DavidM42/channel4/user/video_broadcast.c

/******************************************************************************
 * Copyright 2013-2015 Espressif Systems
 *           2015 <>< Charles Lohr
 * 			 2022 Paul Schlarmann
 *
 * FileName: i2s_freertos.c
 *
 * Description: I2S output routines for a FreeRTOS system. Uses DMA and a queue
 * to abstract away the nitty-gritty details.
 *
 * Modification history:
 *     2015/06/01, v1.0 File created.
 *     2015/07/23, Switch to making it a WS2812 output device.
 *     2016/01/28, Modified to re-include TX_ stuff.
 *     2022/09/26, Modified CNLohrs code to also allow PAL broadcast
*******************************************************************************

Notes:

 This is pretty badly hacked together from the MP3 example.
 I spent some time trying to strip it down to avoid a lot of the TX_ stuff. 
 That seems to work.

 Major suggestions that I couldn't figure out:
	* Use interrupts to disable DMA, so it isn't running nonstop.
    * Use interrupts to flag when new data can be sent.

 When I try using interrupts, it seems to work for a bit but things fall apart
 rather quickly and the engine just refuses to send anymore until reboot.

 The way it works right now is to keep the DMA running forever and just update
 the data in the buffer so it continues sending the frame.

Extra copyright info:
  Actually not much of this file is Copyright Espressif, comparativly little
  mostly just the stuff to make the I2S bus go.

*******************************************************************************/


#include "slc_register.h"
#include "esp82xxutil.h"
#include <c_types.h>
#include "video_broadcast.h"
#include "user_interface.h"
#include "../tablemaker/broadcast_tables.h"
#include <dmastuff.h>

#define FUNC_I2SO_DATA                      1
#define FUNC_U0RXD                          0  //What the pin is after reset: the UART's receive line.

#define WS_I2S_BCK 1  //Can't be less than 1.
#define WS_I2S_DIV 2

#ifdef PAL
  #define LINE_BUFFER_LENGTH 160

  /* PAL signals */
  #define SHORT_SYNC_INTERVAL    5
  #define LONG_SYNC_INTERVAL    75
  #define NORMAL_SYNC_INTERVAL  10
  #define LINE_SIGNAL_INTERVAL 150

  #define COLORBURST_INTERVAL 10
#else
  #define LINE_BUFFER_LENGTH 159

  /* NTSC signals */
  #define SHORT_SYNC_INTERVAL    6
  #define LONG_SYNC_INTERVAL    73
  #define SERRATION_PULSE_INT   67
  #define NORMAL_SYNC_INTERVAL  12
  #define LINE_SIGNAL_INTERVAL 147

  #define COLORBURST_INTERVAL 4
#endif

//Sync, colorburst and black before the framebuffer starts on a line.
#define HDR_SPD (NORMAL_SYNC_INTERVAL+1+COLORBURST_INTERVAL+11)

//How many picture lines (FT_LIN) the line table in CbTable hands out per field, at least.
#ifdef PAL
  #define PICTURE_LINES 265
#else
  #define PICTURE_LINES 210
#endif

//A framebuffer with fewer lines than that sits in the middle, with black lines above and below it.
#if FBH < PICTURE_LINES
  #define FB_TOP ((PICTURE_LINES-FBH)/2)
#else
  #define FB_TOP 0
#endif

#ifdef WHITE_BORDER
  //Fills the visible area left, right and above the framebuffer with something bright instead of black.  TVs that don't
  //hold their black level (most small black and white ones) show a mostly dark picture as gray, this gives them something
  //bright to go by.  Left/right are in 32-bit words and stay clear of the porches, the top lines skipped are the ones in
  //vertical blanking.  The lines below the picture stay black: bright lines running right up to vertical sync made the
  //whole picture bounce on the TV this was tried on.
  //BORDER_LEVEL is the color to use.  White is the brightest, but it glows.
  #ifndef BORDER_LEVEL
    #define BORDER_LEVEL WHITE_LEVEL
  #endif
  #ifdef PAL
    #define BORDER_LEFT      5
    #define BORDER_RIGHT     7
    #define BORDER_SKIP_TOP 18
  #else
    #define BORDER_LEFT      4
    #define BORDER_RIGHT    10
    #define BORDER_SKIP_TOP 13
  #endif
#endif

#define I2SDMABUFLEN (LINE_BUFFER_LENGTH)		//Length of one buffer, in 32-bit words.
//#define LINE16LEN (I2SDMABUFLEN*2)
#define LINE32LEN I2SDMABUFLEN

//Bit clock @ 80MHz = 12.5ns
//Word clock = 400ns
//Each NTSC line = 15,734.264 Hz.  63556 ns
//Each group of 4 bytes = 

#define LINETYPES 6

int8_t jam_color = -1; 
uint8_t video_transmitting; //Is the TV signal on the RX pin right now?  Set with VideoTransmit().

//WS_I2S_DIV - if 1 will actually be 2.  Can't be less than 2.

//		CLK_I2S = 160MHz / I2S_CLKM_DIV_NUM
//		BCLK = CLK_I2S / I2S_BCK_DIV_NUM
//		WS = BCLK/ 2 / (16 + I2S_BITS_MOD)
//		Note that I2S_CLKM_DIV_NUM must be >5 for I2S data
//		I2S_CLKM_DIV_NUM - 5-127
//		I2S_BCK_DIV_NUM - 2-127



//I2S DMA buffer descriptors
static struct sdio_queue i2sBufDesc[DMABUFFERDEPTH];
uint32_t i2sBD[I2SDMABUFLEN*DMABUFFERDEPTH];

//Queue which contains empty DMA buffers

//This routine is called as soon as the DMA routine has something to tell us. All we
//handle here is the RX_EOF_INT status, which indicate the DMA has sent a buffer whose
//descriptor has the 'EOF' field set to 1.
int gline = 0;
int gframe = 0;
static int linescratch;
uint16_t framebuffer[((FBW2/4)*(FBH))*2];

const uint32_t * tablestart = &premodulated_table[0];
const uint32_t * tablept = &premodulated_table[0];
const uint32_t * tableend = &premodulated_table[PREMOD_ENTRIES*PREMOD_SIZE];
uint32_t * curdma;

uint16_t pixline; //line number currently being written out.  PAL has more than 255 of them.
#ifdef WHITE_BORDER
uint8_t marginline; //how many of the margin lines above the picture are out already.
#endif

//Each "qty" is 32 bits, or .4us
LOCAL void fillwith( uint16_t qty, uint8_t color )
{
//	return;
	//We're using this one.
	if( qty & 1 )
	{
		*(curdma++) = tablept[color]; tablept += PREMOD_SIZE;
	}
	qty>>=1;
	for( linescratch = 0; linescratch < qty; linescratch++ )
	{
		*(curdma++) = tablept[color]; tablept += PREMOD_SIZE;
		*(curdma++) = tablept[color]; tablept += PREMOD_SIZE;
		if( tablept >= tableend ) tablept = tablept - tableend + tablestart;
	}
}


//XXX TODO: Revisit the length of time the system is at SYNC, BLACK, etc.

LOCAL void FT_STA() // Short Sync
{
	pixline = 0; //Reset the framebuffer out line count (can be done multiple times)
#ifdef WHITE_BORDER
	marginline = 0;
#endif

	fillwith( SHORT_SYNC_INTERVAL, SYNC_LEVEL );
	fillwith( LONG_SYNC_INTERVAL, BLACK_LEVEL );
	fillwith( SHORT_SYNC_INTERVAL, SYNC_LEVEL );
	fillwith( LINE32LEN - (SHORT_SYNC_INTERVAL+LONG_SYNC_INTERVAL+SHORT_SYNC_INTERVAL), BLACK_LEVEL );
}


LOCAL void FT_STB() // Long Sync
{
	#ifdef PAL
		#define FT_STB_BLACK_INTERVAL SHORT_SYNC_INTERVAL
	#else
		#define FT_STB_BLACK_INTERVAL NORMAL_SYNC_INTERVAL
	#endif
	fillwith( LONG_SYNC_INTERVAL, SYNC_LEVEL );
	fillwith( FT_STB_BLACK_INTERVAL, BLACK_LEVEL );
	fillwith( LONG_SYNC_INTERVAL, SYNC_LEVEL );
	fillwith( LINE32LEN - (LONG_SYNC_INTERVAL+FT_STB_BLACK_INTERVAL+LONG_SYNC_INTERVAL), BLACK_LEVEL );
}

//Margin at top and bottom of screen (Mostly invisible)
//Closed Captioning would go somewhere in here, I guess?
LOCAL void FT_B() // Black
{
	fillwith( NORMAL_SYNC_INTERVAL, SYNC_LEVEL );
	fillwith( 2, BLACK_LEVEL );
	fillwith( COLORBURST_INTERVAL, COLORBURST_LEVEL );
#ifdef WHITE_BORDER
	//Above the picture and past vertical blanking.
	if( !pixline && marginline++ >= BORDER_SKIP_TOP )
	{
		fillwith( 10 - BORDER_LEFT, BLACK_LEVEL );
		fillwith( BORDER_LEFT + FBW2 + BORDER_RIGHT, BORDER_LEVEL );
		fillwith( LINE32LEN - (HDR_SPD+FBW2+BORDER_RIGHT), BLACK_LEVEL );
		return;
	}
#endif
	fillwith( LINE32LEN-NORMAL_SYNC_INTERVAL-2-COLORBURST_INTERVAL, (pixline<1)?GRAY_LEVEL:BLACK_LEVEL);
	//Gray seems to help sync if at top.  TODO: Investigate if white works even better!
}

LOCAL void FT_SRA() // Short to long
{
	fillwith( SHORT_SYNC_INTERVAL, SYNC_LEVEL );
	fillwith( LONG_SYNC_INTERVAL, BLACK_LEVEL );
	#ifdef PAL
	fillwith( LONG_SYNC_INTERVAL, SYNC_LEVEL );
	fillwith( LINE32LEN - (SHORT_SYNC_INTERVAL+LONG_SYNC_INTERVAL+LONG_SYNC_INTERVAL), BLACK_LEVEL );
	#else
	fillwith( SERRATION_PULSE_INT, SYNC_LEVEL );
	fillwith( LINE32LEN - (SHORT_SYNC_INTERVAL+LONG_SYNC_INTERVAL+SERRATION_PULSE_INT), BLACK_LEVEL );
	#endif
}

LOCAL void FT_SRB() // Long to short
{
	#ifdef PAL
	fillwith( LONG_SYNC_INTERVAL, SYNC_LEVEL );
	fillwith( SHORT_SYNC_INTERVAL, BLACK_LEVEL );
	fillwith( SHORT_SYNC_INTERVAL, SYNC_LEVEL );
	fillwith( LINE32LEN - (LONG_SYNC_INTERVAL+SHORT_SYNC_INTERVAL+SHORT_SYNC_INTERVAL), BLACK_LEVEL );
	#else
	fillwith( SERRATION_PULSE_INT, SYNC_LEVEL );
	fillwith( NORMAL_SYNC_INTERVAL, BLACK_LEVEL );
	fillwith( SHORT_SYNC_INTERVAL, SYNC_LEVEL );
	fillwith( LINE32LEN - (SERRATION_PULSE_INT+NORMAL_SYNC_INTERVAL+SHORT_SYNC_INTERVAL), BLACK_LEVEL );
	#endif
}

LOCAL void FT_LIN() // Line Signal
{
	//TODO: Make this do something useful.
	fillwith( NORMAL_SYNC_INTERVAL, SYNC_LEVEL );
	fillwith( 1, BLACK_LEVEL );
	fillwith( COLORBURST_INTERVAL, COLORBURST_LEVEL );

#if FBH < PICTURE_LINES
	//Lines the framebuffer does not reach, above and below it.
	if( (uint16_t)( pixline - FB_TOP ) >= FBH )
	{
#ifdef WHITE_BORDER
		if( pixline < FB_TOP )
		{
			fillwith( 11 - BORDER_LEFT, BLACK_LEVEL );
			fillwith( BORDER_LEFT + FBW2 + BORDER_RIGHT, BORDER_LEVEL );
			fillwith( LINE32LEN - (HDR_SPD+FBW2+BORDER_RIGHT), BLACK_LEVEL );
		}
		else
#endif
		{
			fillwith( LINE32LEN - (HDR_SPD-11), BLACK_LEVEL );
		}
		pixline++;
		return;
	}
#endif

#ifdef WHITE_BORDER
	fillwith( 11 - BORDER_LEFT, BLACK_LEVEL );
	fillwith( BORDER_LEFT, BORDER_LEVEL );
#else
	fillwith( 11, BLACK_LEVEL );
#endif

	int fframe = gframe & 1;
//#define FILLTEST
#ifdef FILLTEST

	fillwith( FBW/32, BLACK_LEVEL );
	fillwith( FBW/32, 1 );
	fillwith( FBW/32, 2 );
	fillwith( FBW/32, 3 );
	fillwith( FBW/32, 4 );
	fillwith( FBW/32, 5 );
	fillwith( FBW/32, 6 );
	fillwith( FBW/32, 0 );
	fillwith( FBW/32, 0 );
	fillwith( FBW/32, 0 );
	fillwith( FBW/32, 0 );
	fillwith( FBW/32, 0 );
	fillwith( FBW/8, BLACK_LEVEL );
	fillwith( LINE32LEN - (HDR_SPD+FBW/2), BLACK_LEVEL );

#else
	uint16_t * fbs = (uint16_t*)(&framebuffer[ ( ((pixline-FB_TOP) * (FBW2/2)) + ( ((FBW2/2)*(FBH))*(fframe)) ) / 2 ]);

	for( linescratch = 0; linescratch < FBW2/4; linescratch++ )
	{
		uint16_t fbb;
		fbb = fbs[linescratch];
		*(curdma++) = tablept[(fbb>>0)&15];		tablept += PREMOD_SIZE;
		*(curdma++) = tablept[(fbb>>4)&15];		tablept += PREMOD_SIZE;
		*(curdma++) = tablept[(fbb>>8)&15];		tablept += PREMOD_SIZE;
		*(curdma++) = tablept[(fbb>>12)&15];	tablept += PREMOD_SIZE;
		if( tablept >= tableend ) tablept = tablept - tableend + tablestart;
	}

#ifdef WHITE_BORDER
	fillwith( BORDER_RIGHT, BORDER_LEVEL );
	fillwith( LINE32LEN - (HDR_SPD+FBW2+BORDER_RIGHT), BLACK_LEVEL );
#else
	fillwith( LINE32LEN - (HDR_SPD+FBW2), BLACK_LEVEL); //WHITE_LEVEL );
#endif
#endif

	pixline++;
}

static uint32_t systimex = 0;
static uint32_t systimein = 0;
uint32_t last_internal_frametime;
LOCAL void FT_CLOSE_M() // End Frame
{
	#ifdef PAL
	fillwith( SHORT_SYNC_INTERVAL, SYNC_LEVEL );
	fillwith( LONG_SYNC_INTERVAL, BLACK_LEVEL );
	fillwith( SHORT_SYNC_INTERVAL, SYNC_LEVEL );
	fillwith( LINE32LEN - (SHORT_SYNC_INTERVAL+LONG_SYNC_INTERVAL+SHORT_SYNC_INTERVAL), BLACK_LEVEL );
	#else
	fillwith( NORMAL_SYNC_INTERVAL, SYNC_LEVEL );
	fillwith( 2, BLACK_LEVEL );
	fillwith( 4, COLORBURST_LEVEL );
	fillwith( LINE32LEN-NORMAL_SYNC_INTERVAL-6, WHITE_LEVEL );
	#endif
	gline = -1;
	gframe++;

	last_internal_frametime = systimex;
	systimex = 0;
	systimein = system_get_time();
}

#include "../tablemaker/CbTable.h" 

void (*CbTable[FT_MAX_d])() = { FT_STA, FT_STB, FT_B, FT_SRA, FT_SRB, FT_LIN, FT_CLOSE_M };

void slc_isr(void * v) {
	//portBASE_TYPE HPTaskAwoken=0;
	struct sdio_queue *finishedDesc;
	uint32 slc_intr_status;
	int x;

	slc_intr_status = READ_PERI_REG(SLC_INT_STATUS);
	//clear all intr flags
	WRITE_PERI_REG(SLC_INT_CLR, 0xffffffff);//slc_intr_status);
	if ( (slc_intr_status & SLC_RX_EOF_INT_ST))
	{
		//The DMA subsystem is done with this block: Push it on the queue so it can be re-used.
		finishedDesc=(struct sdio_queue*)READ_PERI_REG(SLC_RX_EOF_DES_ADDR);
		curdma = (uint32_t*)finishedDesc->buf_ptr;

		//Allow signal jamming, useful for testing output.
		if( jam_color < 0 )
		{
			//*startdma = premodulated_table[0];
			int lk = 0;
			if( gline & 1 )
				lk = (CbLookup[gline>>1]>>4)&0x0f;
			else
				lk = CbLookup[gline>>1]&0x0f;
	
			systimein = system_get_time();
			CbTable[lk]();
			systimex += system_get_time() - systimein;
			gline++;
		}
		else
		{
			fillwith( LINE32LEN, jam_color );
		}
	}
}

//Switches the TV signal on the RX pin on or off.
//The line generator keeps running either way, so the signal is there at once when it is switched on.  Off means the
//pin goes back to being the UART's receive line, so it carries no signal: the TV gets nothing, and the board's own
//WiFi is not disturbed by it.  While it is off, no screens get drawn either (see procTask in user_main.c).
void ICACHE_FLASH_ATTR VideoTransmit( int on )
{
	video_transmitting = on ? 1 : 0;

	if( on )
	{
		PIN_FUNC_SELECT(PERIPHS_IO_MUX_U0RXD_U, FUNC_I2SO_DATA);
	}
	else
	{
		PIN_FUNC_SELECT(PERIPHS_IO_MUX_U0RXD_U, FUNC_U0RXD);
	}
}

#ifdef RELAY_GPIO
#if RELAY_GPIO < 0 || RELAY_GPIO > 15 || RELAY_GPIO == 1 || RELAY_GPIO == 3 || ( RELAY_GPIO >= 6 && RELAY_GPIO <= 11 )
#error RELAY_GPIO has to be one of 0, 2, 4, 5, 12, 13, 14, 15.  1 and 3 are the serial lines (3 carries the TV signal), 6 to 11 belong to the flash chip.
#endif

//Switches the relay.  It is not tied to the TV signal: the signal goes off and on while a screen is filled
//(CH and CG), and the relay has to stay on through that.
void ICACHE_FLASH_ATTR RelaySet( int on )
{
	MakePinGPIO( RELAY_GPIO );
	GPIO_OUTPUT_SET( GPIO_ID_PIN( RELAY_GPIO ), on ? 1 : 0 );
}
#endif

//Initialize I2S subsystem for DMA circular buffer use
void ICACHE_FLASH_ATTR testi2s_init() {
	int x = 0, y;

	jam_color = -1;
/*	
	uint32_t endiantest[1] = { 0xAABBCCDD };
	uint8_t * et = (uint8_t*)endiantest;
	printf( "%02x %02x %02x %02x\n", et[0], et[1], et[2], et[3] );
*/

	//Bits are shifted out

	//Initialize DMA buffer descriptors in such a way that they will form a circular
	//buffer.
	for (x=0; x<DMABUFFERDEPTH; x++) {
		i2sBufDesc[x].owner=1;
		i2sBufDesc[x].eof=1;
		i2sBufDesc[x].sub_sof=0;
		i2sBufDesc[x].datalen=I2SDMABUFLEN*4;
		i2sBufDesc[x].blocksize=I2SDMABUFLEN*4;
		i2sBufDesc[x].buf_ptr=(uint32_t)&i2sBD[x*I2SDMABUFLEN];
		i2sBufDesc[x].unused=0;
		i2sBufDesc[x].next_link_ptr=(int)((x<(DMABUFFERDEPTH-1))?(&i2sBufDesc[x+1]):(&i2sBufDesc[0]));
	}


	//Reset DMA
	SET_PERI_REG_MASK(SLC_CONF0, SLC_RXLINK_RST|SLC_TXLINK_RST);
	CLEAR_PERI_REG_MASK(SLC_CONF0, SLC_RXLINK_RST|SLC_TXLINK_RST);

	//Clear DMA int flags
	SET_PERI_REG_MASK(SLC_INT_CLR,  0xffffffff);
	CLEAR_PERI_REG_MASK(SLC_INT_CLR,  0xffffffff);

	//Enable and configure DMA
	CLEAR_PERI_REG_MASK(SLC_CONF0, (SLC_MODE<<SLC_MODE_S));
	SET_PERI_REG_MASK(SLC_CONF0,(1<<SLC_MODE_S));
	SET_PERI_REG_MASK(SLC_RX_DSCR_CONF,SLC_INFOR_NO_REPLACE|SLC_TOKEN_NO_REPLACE);
	CLEAR_PERI_REG_MASK(SLC_RX_DSCR_CONF, SLC_RX_FILL_EN|SLC_RX_EOF_MODE | SLC_RX_FILL_MODE);
	
	//Feed dma the 1st buffer desc addr
	//To send data to the I2S subsystem, counter-intuitively we use the RXLINK part, not the TXLINK as you might
	//expect. The TXLINK part still needs a valid DMA descriptor, even if it's unused: the DMA engine will throw
	//an error at us otherwise. Just feed it any random descriptor.
	CLEAR_PERI_REG_MASK(SLC_TX_LINK,SLC_TXLINK_DESCADDR_MASK);
	SET_PERI_REG_MASK(SLC_TX_LINK, ((uint32)&i2sBufDesc[1]) & SLC_TXLINK_DESCADDR_MASK); //any random desc is OK, we don't use TX but it needs something valid
	CLEAR_PERI_REG_MASK(SLC_RX_LINK,SLC_RXLINK_DESCADDR_MASK);
	SET_PERI_REG_MASK(SLC_RX_LINK, ((uint32)&i2sBufDesc[0]) & SLC_RXLINK_DESCADDR_MASK);

	//Attach the DMA interrupt
	ets_isr_attach(ETS_SLC_INUM, slc_isr, 0);
	//Enable DMA operation intr
	WRITE_PERI_REG(SLC_INT_ENA,  SLC_RX_EOF_INT_ENA);
	//clear any interrupt flags that are set
	WRITE_PERI_REG(SLC_INT_CLR, 0xffffffff);
	///enable DMA intr in cpu
	ets_isr_unmask(1<<ETS_SLC_INUM);

	//We use a queue to keep track of the DMA buffers that are empty. The ISR will push buffers to the back of the queue,
	//the mp3 decode will pull them from the front and fill them. For ease, the queue will contain *pointers* to the DMA
	//buffers, not the data itself. The queue depth is one smaller than the amount of buffers we have, because there's
	//always a buffer that is being used by the DMA subsystem *right now* and we don't want to be able to write to that
	//simultaneously.
	//dmaQueue=xQueueCreate(I2SDMABUFCNT-1, sizeof(int*));

	//Start transmission
	SET_PERI_REG_MASK(SLC_TX_LINK, SLC_TXLINK_START);
	SET_PERI_REG_MASK(SLC_RX_LINK, SLC_RXLINK_START);

//----

	//Init pins to i2s functions
#ifdef START_SILENT
	//No signal until a command asks for something to be shown (see custom_commands.c)
	VideoTransmit( 0 );
	RelaySet( 0 );
#else
	VideoTransmit( 1 );
	RelaySet( 1 );
#endif
//	PIN_FUNC_SELECT(PERIPHS_IO_MUX_GPIO2_U, FUNC_I2SO_WS);
//	PIN_FUNC_SELECT(PERIPHS_IO_MUX_MTDO_U, FUNC_I2SO_BCK);

	//Enable clock to i2s subsystem
	i2c_writeReg_Mask_def(i2c_bbpll, i2c_bbpll_en_audio_clock_out, 1);

	//Reset I2S subsystem
	CLEAR_PERI_REG_MASK(I2SCONF,I2S_I2S_RESET_MASK);
	SET_PERI_REG_MASK(I2SCONF,I2S_I2S_RESET_MASK);
	CLEAR_PERI_REG_MASK(I2SCONF,I2S_I2S_RESET_MASK);

	//Select 16bits per channel (FIFO_MOD=0), no DMA access (FIFO only)
	CLEAR_PERI_REG_MASK(I2S_FIFO_CONF, I2S_I2S_DSCR_EN|(I2S_I2S_RX_FIFO_MOD<<I2S_I2S_RX_FIFO_MOD_S)|(I2S_I2S_TX_FIFO_MOD<<I2S_I2S_TX_FIFO_MOD_S));
	//Enable DMA in i2s subsystem
	SET_PERI_REG_MASK(I2S_FIFO_CONF, I2S_I2S_DSCR_EN);

	//tx/rx binaureal
	CLEAR_PERI_REG_MASK(I2SCONF_CHAN, (I2S_TX_CHAN_MOD<<I2S_TX_CHAN_MOD_S)|(I2S_RX_CHAN_MOD<<I2S_RX_CHAN_MOD_S));

	//Clear int
	SET_PERI_REG_MASK(I2SINT_CLR,   I2S_I2S_TX_REMPTY_INT_CLR|I2S_I2S_TX_WFULL_INT_CLR|
			I2S_I2S_RX_WFULL_INT_CLR|I2S_I2S_PUT_DATA_INT_CLR|I2S_I2S_TAKE_DATA_INT_CLR);
	CLEAR_PERI_REG_MASK(I2SINT_CLR, I2S_I2S_TX_REMPTY_INT_CLR|I2S_I2S_TX_WFULL_INT_CLR|
			I2S_I2S_RX_WFULL_INT_CLR|I2S_I2S_PUT_DATA_INT_CLR|I2S_I2S_TAKE_DATA_INT_CLR);

	//trans master&rece slave,MSB shift,right_first,msb right
	CLEAR_PERI_REG_MASK(I2SCONF, I2S_TRANS_SLAVE_MOD|
						(I2S_BITS_MOD<<I2S_BITS_MOD_S)|
						(I2S_BCK_DIV_NUM <<I2S_BCK_DIV_NUM_S)|
						(I2S_CLKM_DIV_NUM<<I2S_CLKM_DIV_NUM_S));
	SET_PERI_REG_MASK(I2SCONF, I2S_RIGHT_FIRST|I2S_MSB_RIGHT|I2S_RECE_SLAVE_MOD|
						I2S_RECE_MSB_SHIFT|I2S_TRANS_MSB_SHIFT|
						((WS_I2S_BCK&I2S_BCK_DIV_NUM )<<I2S_BCK_DIV_NUM_S)|
						((WS_I2S_DIV&I2S_CLKM_DIV_NUM)<<I2S_CLKM_DIV_NUM_S));

	//No idea if ints are needed...
	//clear int
	SET_PERI_REG_MASK(I2SINT_CLR,   I2S_I2S_TX_REMPTY_INT_CLR|I2S_I2S_TX_WFULL_INT_CLR|
			I2S_I2S_RX_WFULL_INT_CLR|I2S_I2S_PUT_DATA_INT_CLR|I2S_I2S_TAKE_DATA_INT_CLR);
	CLEAR_PERI_REG_MASK(I2SINT_CLR,   I2S_I2S_TX_REMPTY_INT_CLR|I2S_I2S_TX_WFULL_INT_CLR|
			I2S_I2S_RX_WFULL_INT_CLR|I2S_I2S_PUT_DATA_INT_CLR|I2S_I2S_TAKE_DATA_INT_CLR);
	//enable int
	SET_PERI_REG_MASK(I2SINT_ENA,   I2S_I2S_TX_REMPTY_INT_ENA|I2S_I2S_TX_WFULL_INT_ENA|
	I2S_I2S_RX_REMPTY_INT_ENA|I2S_I2S_TX_PUT_DATA_INT_ENA|I2S_I2S_RX_TAKE_DATA_INT_ENA);

	//Start transmission
	SET_PERI_REG_MASK(I2SCONF,I2S_I2S_TX_START);
}
