DavidM42/channel4/user/video_broadcast.h

//Copyright 2016 <>< Charles Lohr, See LICENSE file.
// COPYRIGHT 2022 Paul Schlarmann

#ifndef _VIDEO_BROADCAST_TEST
#define _VIDEO_BROADCAST_TEST

/*
	This is the Video Broadcast code.  To set it up, call testi2s_init.
	This will set up the DMA engine and all the chains for outputting 
	broadcast.

	This is tightly based off of SpriteTM's ESP8266 MP3 Decoder.

	If you change the RF Maps, please call redo_maps, this will make
	the system update all the non-frame data to use the right bit patterns.
*/


//Stuff that should be for the header:

#include <c_types.h>

//Framebuffer width/height
#define FBW 232 //Must be divisible by 8.  These are actually "double-pixels" used for double-resolution monochrome width.
#define FBW2 (FBW/2) //Actual width in true pixels.
//The framebuffer is the biggest thing in RAM: 116 bytes per line, because it is double-buffered.
//220 lines is what NTSC shows.  A PAL picture has room for 264 (OPTS += -DFBH=264 in user.cfg), but those 44 lines
//cost 5 kB, and then the web page runs out of memory while it loads.  A shorter framebuffer is centered on the screen.
#ifndef FBH
#define FBH 220
#endif

#define DMABUFFERDEPTH 3

extern int gframe; //Current frame #
extern uint16_t framebuffer[((FBW2/4)*(FBH))*2]; // /4 = 4 pixels per word (*2 = double buffer)
extern uint32_t last_internal_frametime;
extern int8_t jam_color; //Used to test frequency out
extern uint8_t video_transmitting; //Is the TV signal on the RX pin right now?


void ICACHE_FLASH_ATTR testi2s_init();
void ICACHE_FLASH_ATTR VideoTransmit( int on ); //TV signal on the RX pin on (1) or off (0)

//A relay on the pin RELAY_GPIO from user.cfg, for example for the power of the TV.  High is on.
//Every command that shows or changes something switches it on, and only the command CR switches it off again
//(see custom_commands.c).  Without RELAY_GPIO there is no relay, and this does nothing.
#ifdef RELAY_GPIO
void ICACHE_FLASH_ATTR RelaySet( int on );
#else
#define RelaySet( on )
#endif

#endif
